factoryal/MuseDashCon/design/jpg/back (Medium).jpg

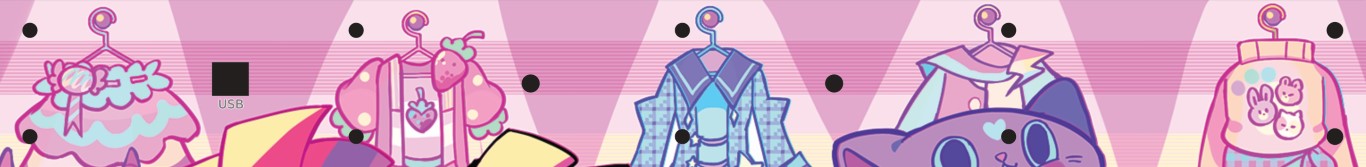
design/jpg/back (Medium).jpg
