factoryal/MuseDashCon/design/jpg/back.jpg

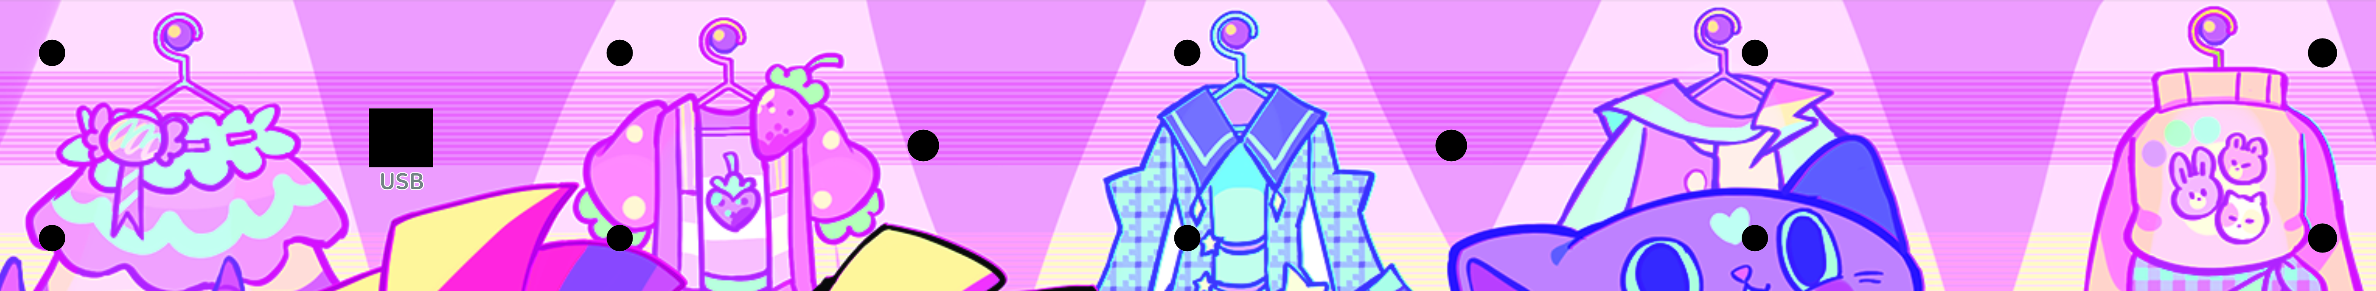
design/jpg/back.jpg
