factoryal/MuseDashCon/design/jpg/right.jpg

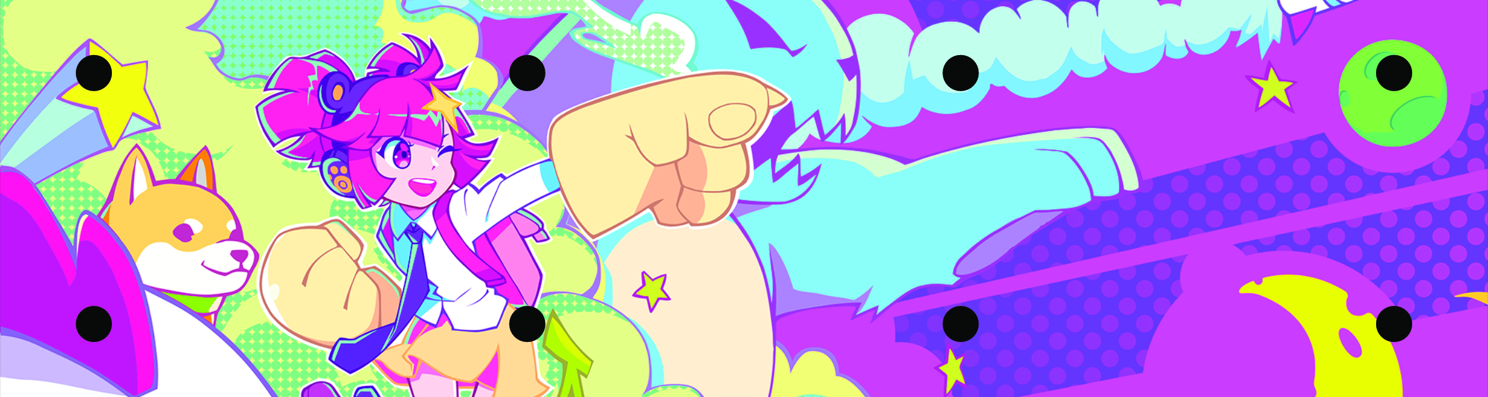
design/jpg/right.jpg
